Anton-Augustsson/micro-computer-server-cases/cad/2u-case/drive-case/ssd-holder.scad

use <ssd-holder-module.scad>;
include <../../utils/constants.scad>;

ssdHolder(c_2uchi,c_2ucho,c_2udbnh,c_cdt);
