Anton-Augustsson/micro-computer-server-cases/cad/2u-case/drive-case/wd-my-passport-holder.scad

use <wd-my-passport-holder-module.scad>;
include <../../utils/constants.scad>;

wdMyPassportHolder(c_2uchi,c_2ucho,c_cdt,c_2udbnh);
