Anton-Augustsson/micro-computer-server-cases/cad/2u-case/2u-case-middle.scad

include <../utils/constants.scad>;
use <../utils/server-rack-node-case/case-middle.scad>;

caseMiddle(c_cwi,c_cwo,c_2uchi,c_2ucho,c_cdt,c_npc,c_2udbnh);
