Anton-Augustsson/micro-computer-server-cases/cad/2u-case/micro-computer-case/raspberry-pi-3-model-b-holder.scad

use <raspberry-pi-3-model-b-holer-module.scad>;
include <../../utils/constants.scad>;

raspberryPi3ModelBtHolder(c_2uchi,c_2ucho);
