Anton-Augustsson/micro-computer-server-cases/cad/2u-case/micro-computer-case/raspberry-pi-4-model-b-holder.scad

use <raspberry-pi-4-model-b-holder-module.scad>;
include <../../utils/constants.scad>;

raspberryPi4ModelBHolder(c_2uchi-1,c_2ucho,c_2udbnh);
