Anton-Augustsson/micro-computer-server-cases/cad/2u-case/miscellaneous/linocell-premium-gan-multiladdare-pd-3-0-100-w-holder.scad

use <linocell-premium-gan-multiladdare-pd-3-0-100-w-holder-module.scad>;
include <../../utils/constants.scad>;

linocellPremiumGanMultiladdarePd30100Wholder(c_2uchi-1,c_2ucho,c_2udbnh);
