Anton-Augustsson/micro-computer-server-cases/cad/utils/server-rack-node-case/case-side.scad

use <case-generic.scad>;

/* caseSide
    case with have rack mounts. One on eatch side

    cwi: case width inner
    cwo: case width outer
    chi: case height inner
    cho: case height outer
    cdt: case depth thickenss
    npc: node per case
    dbnh: distance between node holes
*/
module caseSide(cwi,cwo,chi,cho,cdt,npc,dbnh){
    cst = (cwo-cwi)/2; // case side thickness
    csw = 20; // case side mount width
    csmt = 3; // case side mount thickness
    dfcetmh = 7.56; // distance from case end to mounting hole
    
    s = 1;
    s2 = s*2;

    hds = 7; // hole diameter for serer rack
    dbh = 44.45; // distance between holes

    module serverMountingHoles() {
        play = 4;

        hull() {
          translate([-play/2,0,0]) 
          cylinder(h=csmt,d=hds);

          translate([play/2,0,0]) 
          cylinder(h=csmt,d=hds);
        }
    }

    difference(){
        union(){
            caseGeneric(cwi,cwo,chi,cho,cdt,npc,dbnh,true);

            translate([cwo+cst,0,0])
            cube([csw,cho,csmt]);
        }
        union(){
            translate([cwo+cst+dfcetmh,(cho-dbh)/2,0]) // TODO: change to correct possition
            serverMountingHoles();
            translate([cwo+cst+dfcetmh,(cho+dbh)/2,0]) // TODO: change to correct possition
            serverMountingHoles();

            // Remove 1mm to allow some margin
            translate([cwo+cst-1,0,csmt])
            cube([1,cho,cdt-csmt]);
        }
    }
}
